notaroomba/ember/assets/3D_model.png

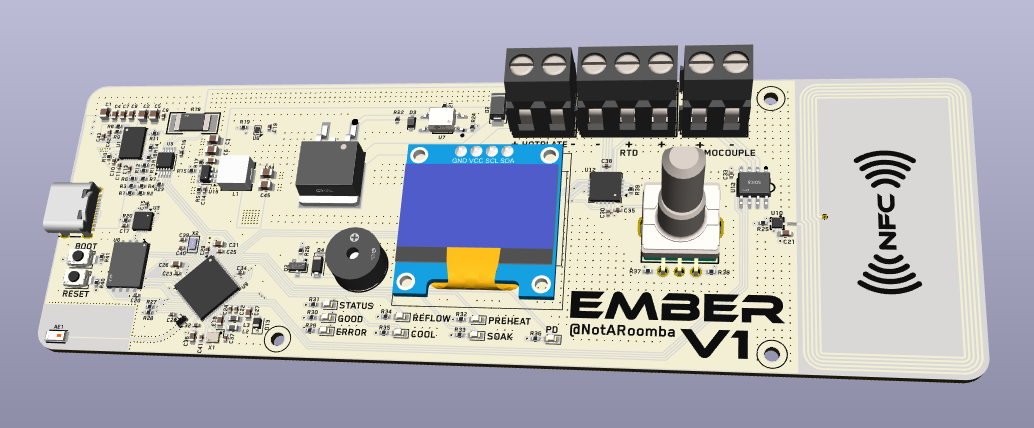
assets/3D_model.png
