notaroomba/ember/assets/aliexpress_1.png

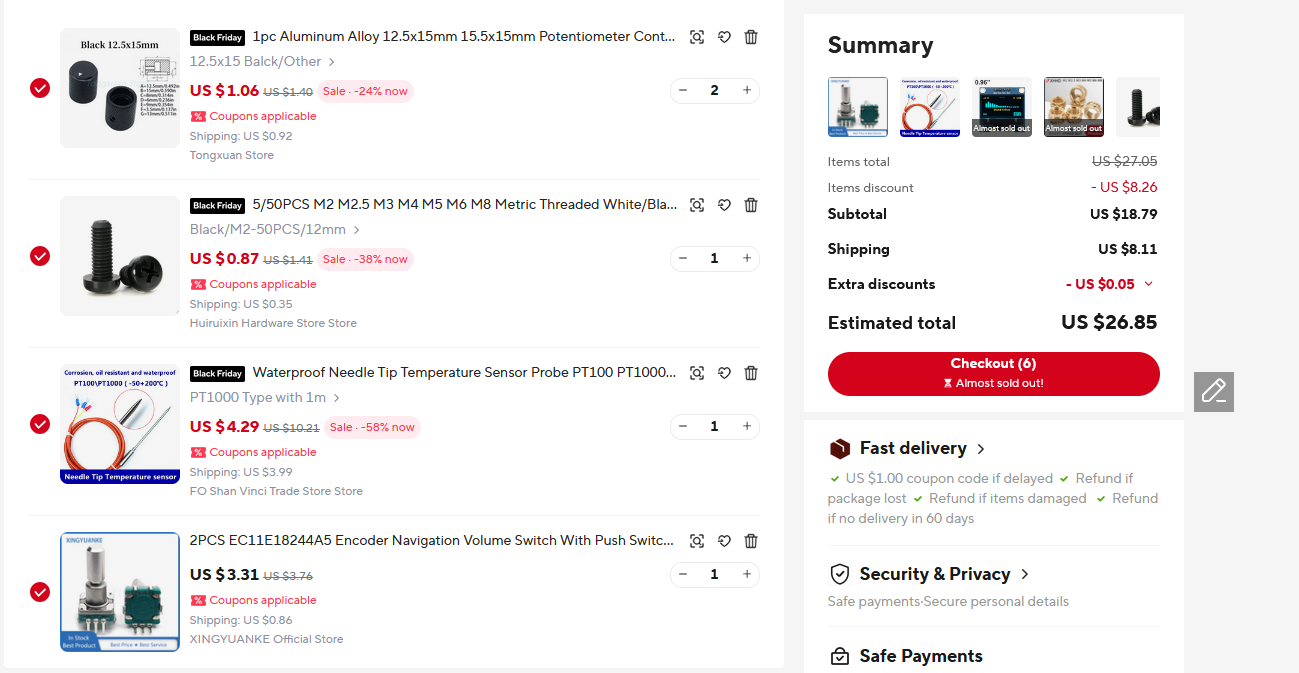
assets/aliexpress_1.png
