notaroomba/ember/assets/aliexpress_2.png

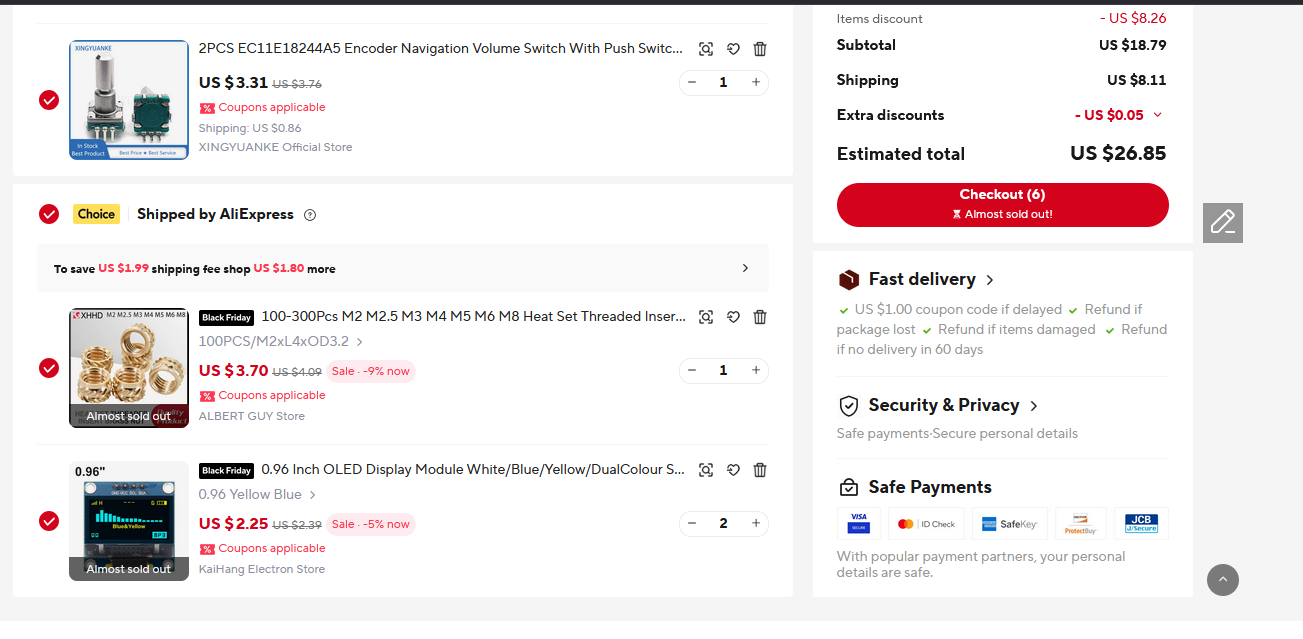
assets/aliexpress_2.png
