notaroomba/ember/assets/ember-In1_Cu.png

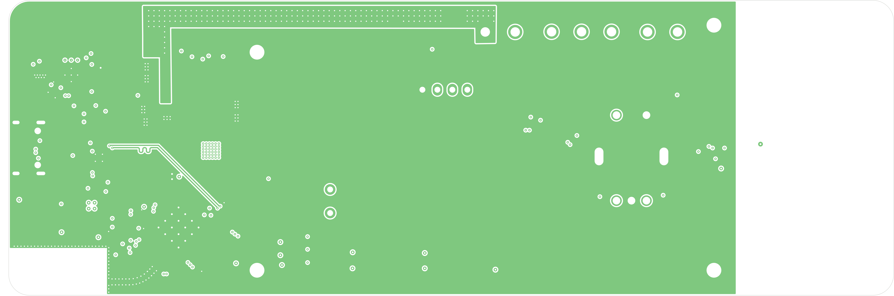
assets/ember-In1_Cu.png
