notaroomba/ember/assets/flyer.png

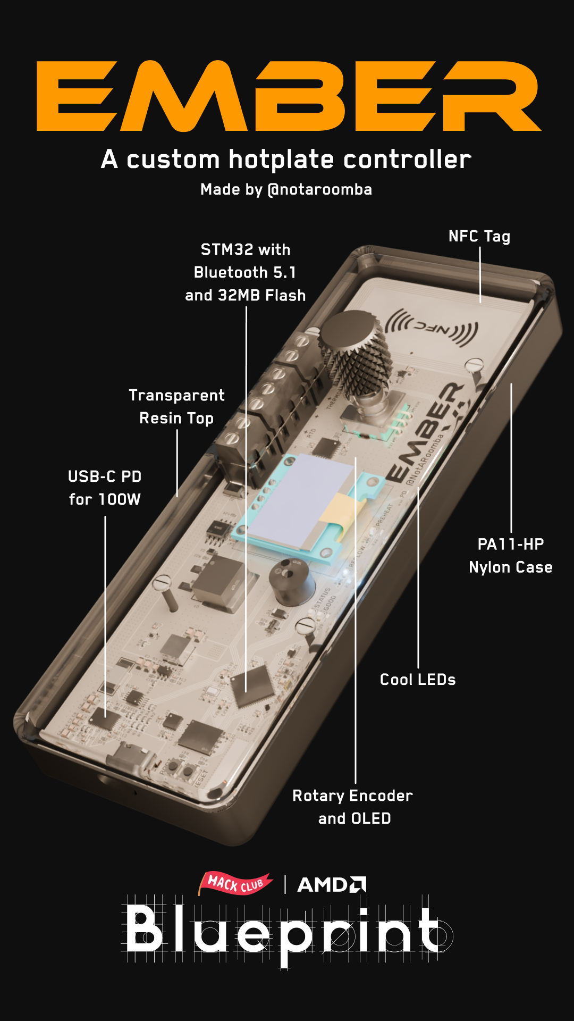
assets/flyer.png
