notaroomba/ember/assets/heatbed.png

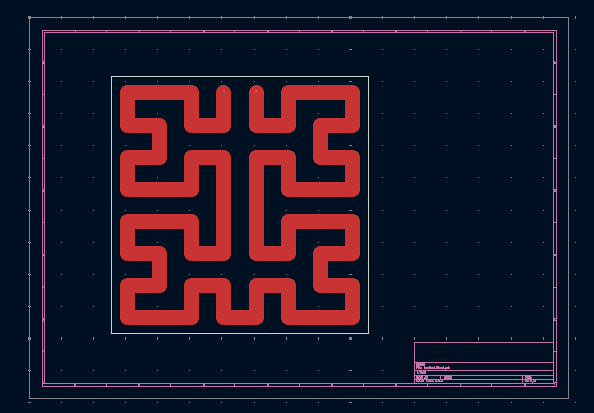
assets/heatbed.png
