notaroomba/ember/assets/jlc_3.png

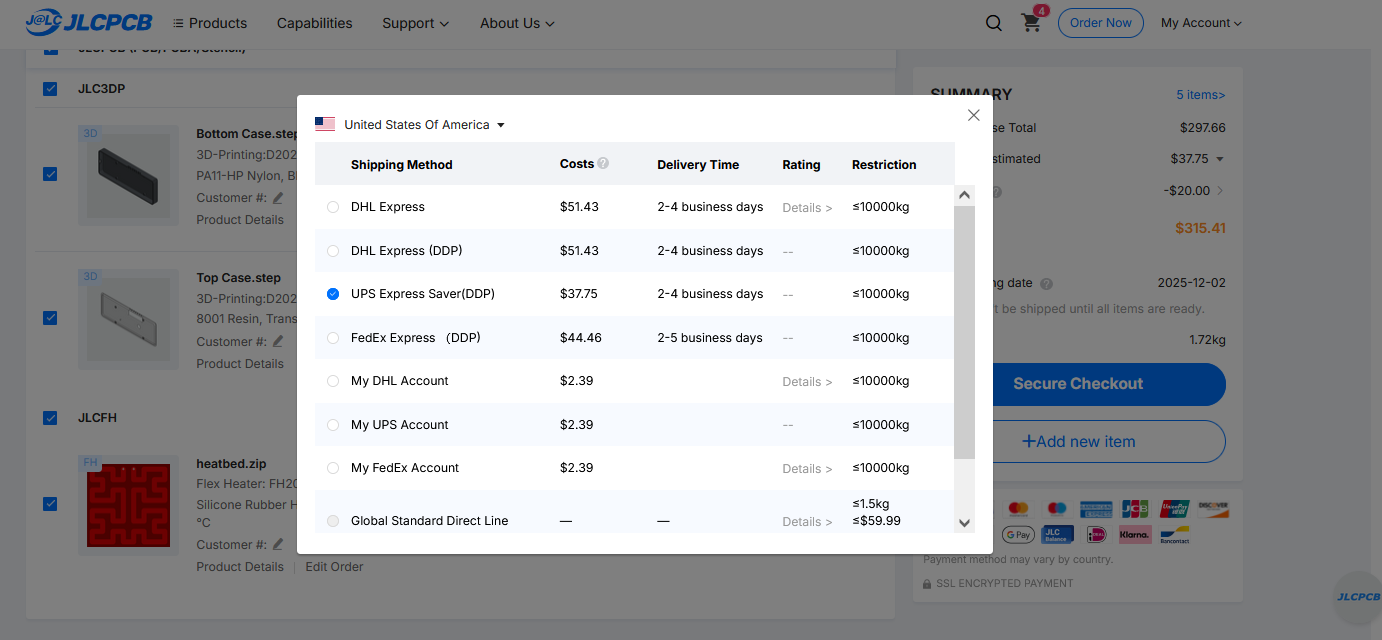
assets/jlc_3.png
